CoretechR/OMOTE/PCB/Remote.kicad_sch

## KiCad design PCB/Remote.kicad_sch (2023-08-01)

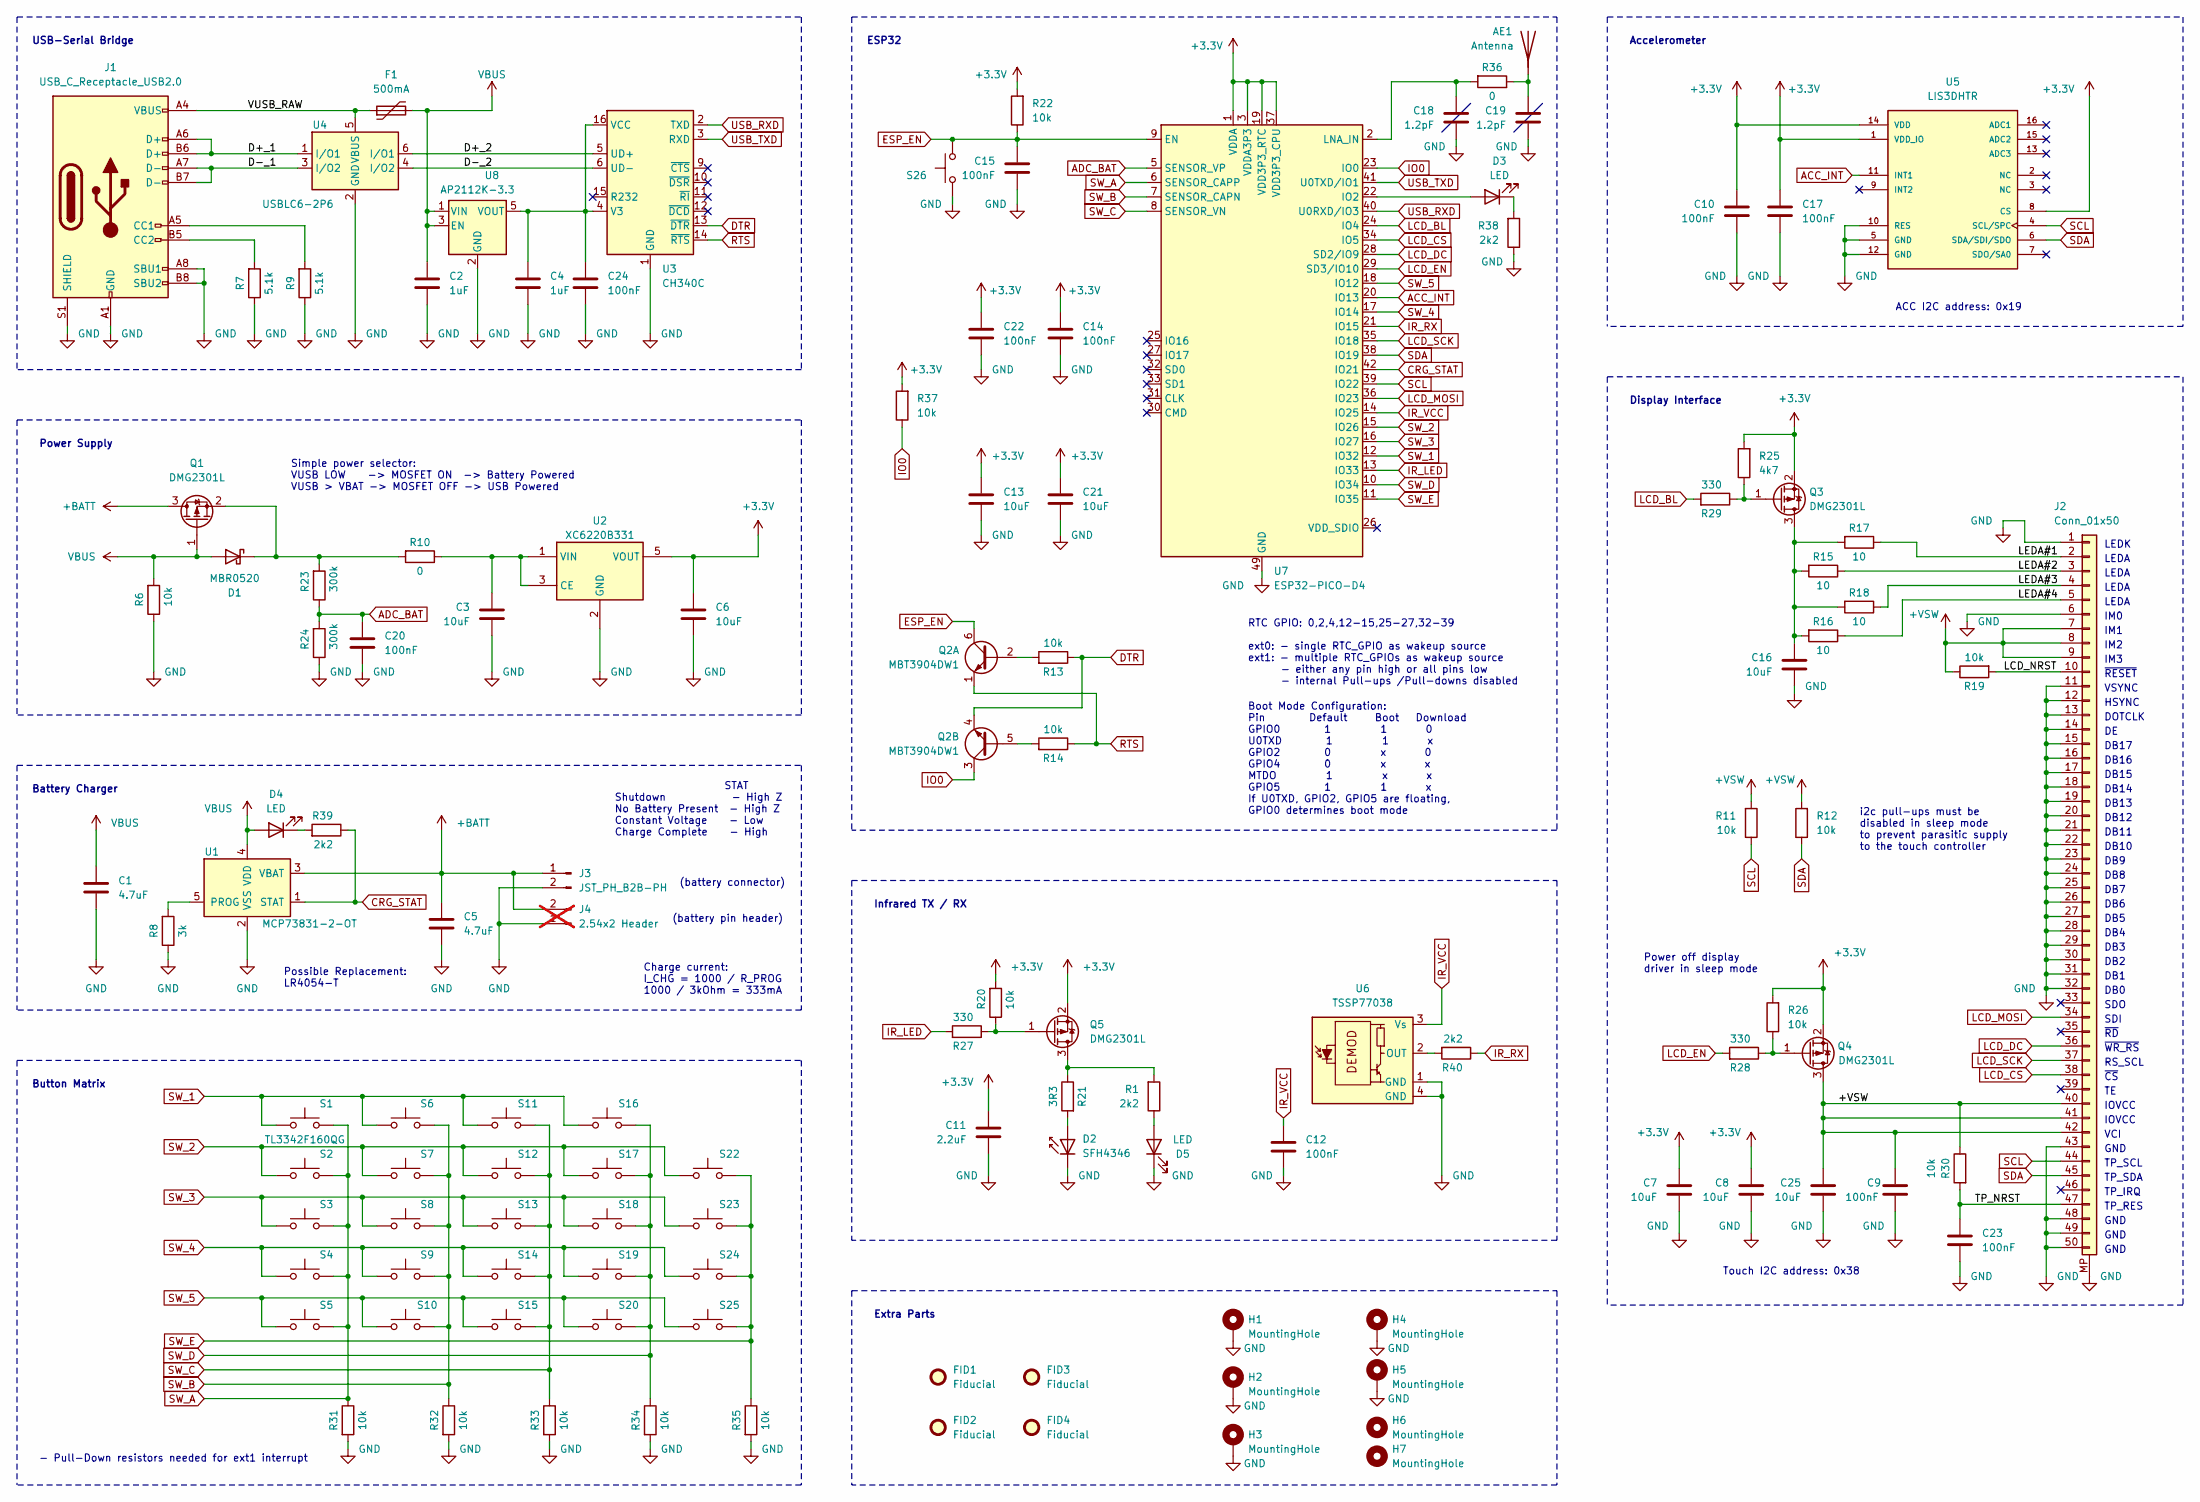
[picture p8: schematic Remote.kicad_sch]

Parts:
AE1: Antenna; RFANT5220110A2T
C1, C5: 4.7uF; C_0603_1608Metric
C2, C4: 1uF; C_0603_1608Metric
C3, C6, C7, C8, C13, C16, C21, C25: 10uF; C_0805_2012Metric
C9, C10, C12, C14, C15, C17, C20, C22, C23, C24: 100nF; C_0603_1608Metric
C11: 2.2uF; C_0603_1608Metric
C18, C19: 1.2pF; C_0603_1608Metric
D1: MBR0520; D_SOD-123
D2: SFH4346; LED_5mm_Side_Mount
D3, D4, D5: LED; LED_0603_1608Metric
F1: 500mA; Fuse_1206_3216Metric_Pad1.42x1.75mm_HandSolder
FID1, FID2, FID3, FID4: Fiducial; Fiducial_1mm_Mask2mm
H1, H2, H3, H4, H5: MountingHole; MountingHole_3.2mm_M3_Pad_Via
H6, H7: MountingHole; MountingHole_2.5mm
J1: USB_C_Receptacle_USB2.0; USB_C_Receptacle_HRO_TYPE-C-31-M-12
J2: Conn_01x50; TFT_2.83IN_240X320_50PIN
J3: JST_PH_B2B-PH; JST_PH_B2B-PH-SM4-TB_1x02-1MP_P2.00mm_Vertical
J4: 2.54x2 Header; PinHeader_1x02_P2.54mm_Vertical; not fitted
Q1, Q3, Q4, Q5: DMG2301L; SOT-23
Q2: MBT3904DW1; SOT-363_SC-70-6
R1, R38, R39, R40: 2k2; R_0603_1608Metric
R6, R11, R12, R13, R14, R19, R20, R22, R26, R30, R31, R32, R33, R34, R35, R37: 10k; R_0603_1608Metric
R7, R9: 5.1k; R_0603_1608Metric
R8: 3k; R_0603_1608Metric
R10, R36: 0; R_0603_1608Metric
R15, R16, R17, R18: 10; R_0603_1608Metric
R21: 3R3; R_0805_2012Metric
R23, R24: 300k; R_0603_1608Metric
R25: 4k7; R_0603_1608Metric
R27, R28, R29: 330; R_0603_1608Metric
S1, S2, S3, S4, S5, S6, S7, S8, S9, S10, S11, S12, S13, S14, S15, S16, S17, S18, S19, S20, S22, S23, S24, S25, S26: TL3342F160QG; SW_SPST_TL3342
U1: MCP73831-2-OT; SOT-23-5
U2: XC6220B331; SOT-23-5
U3: CH340C; SOIC-16_3.9x9.9mm_P1.27mm
U4: USBLC6-2P6; SOT-666
U5: LIS3DHTR; XDCR_LIS3DHTR; PARTREV 2
U6: TSSP77038; Heimdall vertical
U7: ESP32-PICO-D4; QFN-48-1EP_7x7mm_P0.5mm_EP5.3x5.3mm_ThermalVias_MR
U8: AP2112K-3.3; SOT-23-5

Connections:
+3.3V: C6.1, C7.2, C8.2, C10.1, C11.1, C13.2, C14.1, C17.1, C21.2, C22.1, Q3.2 (S), Q4.2 (S), Q5.2 (S), R20.2, R22.2, R25.2, R26.2, R37.2, U2.5 (VOUT), U5.1 (VDD_IO), U5.8 (CS), U5.14 (VDD), U7.1 (VDDA), U7.3 (VDDA3P3), U7.4 (VDDA3P3), U7.19 (VDD3P3_RTC), U7.37 (VDD3P3_CPU), U7.43 (VDDA), U7.46 (VDDA)
+BATT: C5.2, J3.1, J4.2, Q1.3 (D), U1.3 (VBAT)
+VSW: C9.1, C25.2, J2.7, J2.8, J2.9, J2.40, J2.41, J2.42 (Pin_41), Q4.3 (D), R11.2, R12.2, R19.1, R30.1
ACC_INT: U5.11 (INT1), U7.20 (IO13)
ADC_BAT: C20.1, R23.1, R24.2, U7.5 (SENSOR_VP)
CRG_STAT: R39.1, U1.1 (STAT), U7.42 (IO21)
D+_1: J1.A6 (D+), J1.B6 (D+), U4.1 (I/O1)
D+_2: U3.5 (UD+), U4.6 (I/O1)
D-_1: J1.A7 (D-), J1.B7 (D-), U4.3 (I/O2)
D-_2: U3.6 (UD-), U4.4 (I/O2)
DTR: Q2.4 (E2), R13.1, U3.13 (~DTR)
ESP_EN: C15.2, Q2.6 (C1), R22.1, S26.2, U7.9 (EN)
GND: C1.1, C2.2, C3.1, C4.2, C5.1, C6.2, C7.1, C8.1, C9.2, C10.2, C11.2, C12.2, C13.1, C14.2, C15.1, C16.1, C17.2, C18.1, C19.1, C20.2, C21.1, C22.2, C23.1, C24.2, C25.1, D2.1 (K), D5.1 (K), H1.1, H2.1, H3.1, H4.1, H5.1, J1.A1 (GND), J1.A8 (SBU1), J1.A12 (GND), J1.B1 (GND), J1.B8 (SBU2), J1.B12 (GND), J1.S1 (SHIELD), J2.1, J2.6, J2.11, J2.12, J2.13, J2.14, J2.15, J2.16, J2.17, J2.18, J2.19, J2.20, J2.21, J2.22, J2.23, J2.24, J2.25, J2.26, J2.27, J2.28, J2.29, J2.30, J2.31, J2.32, J2.43, J2.48, J2.49, J2.50, J2.MP, J3.2, J4.1, R6.1, R7.1, R8.1, R9.1, R24.1, R31.2, R32.2, R33.2, R34.2, R35.2, R38.1, S26.1, U1.2 (VSS), U2.2 (GND), U3.1 (GND), U4.2 (GND), U5.5 (GND), U5.10 (RES), U5.12 (GND), U6.1 (GND), U6.4 (GND), U7.49 (GND), U8.2 (GND)
IO0: Q2.3 (C2), R37.1, U7.23 (IO0)
IR_LED: R27.2, U7.13 (IO33)
IR_RX: R40.1, U7.21 (IO15)
IR_VCC: C12.1, U6.3 (Vs), U7.14 (IO25)
LCD_BL: R29.2, U7.24 (IO4)
LCD_CS: J2.38, U7.34 (IO5)
LCD_DC: J2.36, U7.28 (SD2/IO9)
LCD_EN: R28.2, U7.29 (SD3/IO10)
LCD_MOSI: J2.34, U7.36 (IO23)
LCD_NRST: J2.10, R19.2
LCD_SCK: J2.37, U7.35 (IO18)
LEDA#1: J2.2, R17.1
LEDA#2: J2.3, R15.1
LEDA#3: J2.4, R18.1
LEDA#4: J2.5, R16.1
unnamed: AE1.1, C19.2, R36.1
unnamed: C3.2, R10.1, U2.1 (VIN), U2.3 (CE)
unnamed: C16.2, Q3.3 (D), R15.2, R16.2, R17.2, R18.2
unnamed: C18.2, R36.2, U7.2 (LNA_IN)
unnamed: C4.1, C24.1, U3.4 (V3), U3.16 (VCC), U8.5 (VOUT)
unnamed: D1.1 (K), Q1.2 (S), R10.2, R23.2
unnamed: D2.2 (A), R21.2
unnamed: D3.1 (K), R38.2
unnamed: D3.2 (A), U7.22 (IO2)
unnamed: D4.1 (K), R39.2
unnamed: D5.2 (A), R1.1
unnamed: J1.A5 (CC1), R9.2
unnamed: J1.B5 (CC2), R7.2
unnamed: Q2.2 (B1), R13.2
unnamed: Q2.5 (B2), R14.2
unnamed: Q3.1 (G), R25.1, R29.1
unnamed: Q4.1 (G), R26.1, R28.1
unnamed: Q5.1 (G), R20.1, R27.1
unnamed: Q5.3 (D), R1.2, R21.1
unnamed: R8.2, U1.5 (PROG)
unnamed: R40.2, U6.2 (OUT)
RTS: Q2.1 (E1), R14.1, U3.14 (~RTS)
SCL: J2.44, R11.1, U5.4 (SCL/SPC), U7.39 (IO22)
SDA: J2.45, R12.1, U5.6 (SDA/SDI/SDO), U7.38 (IO19)
SW_1: S1.1, S6.1, S11.1, S16.1, U7.12 (IO32)
SW_2: S2.1, S7.1, S12.1, S17.1, S22.1, U7.15 (IO26)
SW_3: S3.1, S8.1, S13.1, S18.1, S23.1, U7.16 (IO27)
SW_4: S4.1, S9.1, S14.1, S19.1, S24.1, U7.17 (IO14)
SW_5: S5.1, S10.1, S15.1, S20.1, S25.1, U7.18 (IO12)
SW_A: R31.1, S1.2, S2.2, S3.2, S4.2, S5.2, U7.6 (SENSOR_CAPP)
SW_B: R32.1, S6.2, S7.2, S8.2, S9.2, S10.2, U7.7 (SENSOR_CAPN)
SW_C: R33.1, S11.2, S12.2, S13.2, S14.2, S15.2, U7.8 (SENSOR_VN)
SW_D: R34.1, S16.2, S17.2, S18.2, S19.2, S20.2, U7.10 (IO34)
SW_E: R35.1, S22.2, S23.2, S24.2, S25.2, U7.11 (IO35)
TP_NRST: C23.2, J2.47, R30.2
USB_RXD: U3.2 (TXD), U7.40 (U0RXD/IO3)
USB_TXD: U3.3 (RXD), U7.41 (U0TXD/IO1)
VBUS: C1.2, C2.1, D1.2 (A), D4.2 (A), F1.2, Q1.1 (G), R6.2, U1.4 (VDD), U8.1 (VIN), U8.3 (EN)
VUSB_RAW: F1.1, J1.A4 (VBUS), J1.A9 (VBUS), J1.B4 (VBUS), J1.B9 (VBUS), U4.5 (VBUS)

Notes on the sheet:
DB6
ACC I2C address: 0x19
DB11
DB14
IM2
DB10
Display Interface
STAT Shutdown - High Z No Battery Present - High Z Constant Voltage - Low Charge Complete - High
LEDA
DB0
GND
DB16
TP_RES
TP_IRQ
LEDK
IM1
IOVCC
- Pull-Down resistors needed for ext1 interrupt
~{RESET}
ESP32
RTC GPIO: 0,2,4,12-15,25-27,32-39 ext0: - single RTC_GPIO as wakeup source ext1: - multiple RTC_GPIOs as wakeup source - either any pin high or all pins low - internal Pull-ups /Pull-downs disabled
IM3
DB5
Possible Replacement: LR4054-T
Extra Parts
USB-Serial Bridge
Charge current: I_CHG = 1000 / R_PROG 1000 / 3kOhm = 333mA
DB17
TP_SDA
DB7
DB12
DB1
DOTCLK
~{WR_RS}
Infrared TX / RX
SDI
DB13
DB4
Boot Mode Configuration: Pin Default Boot Download GPIO0 1 1 0 U0TXD 1 1 x GPIO2 0 x 0 GPIO4 0 x x MTDO 1 x x GPIO5 1 1 x If U0TXD, GPIO2, GPIO5 are floating, GPIO0 determines boot mode
Touch I2C address: 0x38
VCI
Battery Charger
Power Supply
Power off display driver in sleep mode
i2c pull-ups must be disabled in sleep mode to prevent parasitic supply to the touch controller
DB15
Button Matrix
VSYNC
DB2
(battery pin header)
DB9
(battery connector)
Simple power selector: VUSB LOW -> MOSFET ON -> Battery Powered VUSB > VBAT -> MOSFET OFF -> USB Powered
RS_SCL
TP_SCL
IM0
SDO
~{RD}
DB3
~{CS}
DB8
HSYNC
Accelerometer
