CoretechR/OMOTE/hardware/ESP32/sd_card_hal_esp32.h

#pragma once

extern const uint8_t SD_EN_GPIO;
extern const uint8_t SD_CS_GPIO;
extern const uint8_t SD_MISO_GPIO;
extern const uint8_t SD_MOSI_GPIO;
extern const uint8_t SD_SCK_GPIO;

void init_SD_HAL(void);
